dltech/usb_player/result/player.png

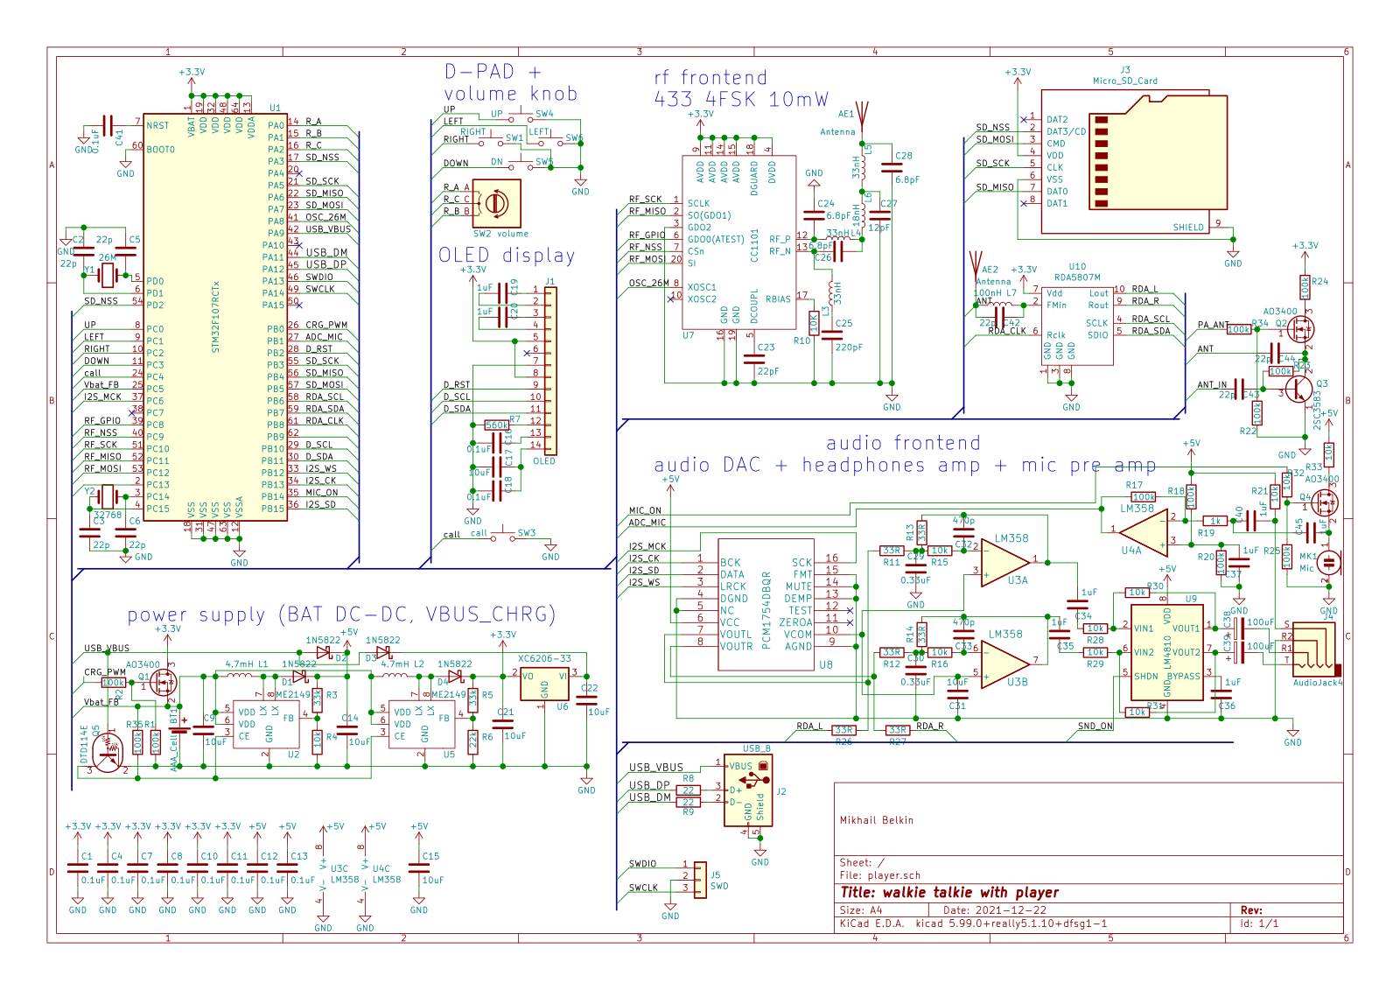
result/player.png
